ImtiazAtBradley/VIP_Weather/images/unor3.jpg

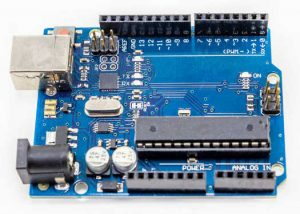
images/unor3.jpg
