ImtiazAtBradley/VIP_Weather/images/antenna-field.gif

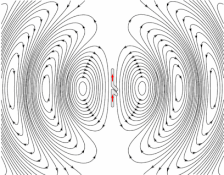
images/antenna-field.gif
