ImtiazAtBradley/VIP_Weather/images/dipole-antenna.gif

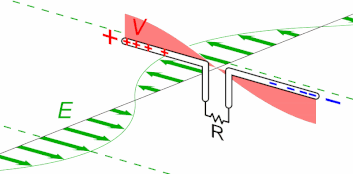
images/dipole-antenna.gif
