ImtiazAtBradley/VIP_Weather/images/esp32block.jpg

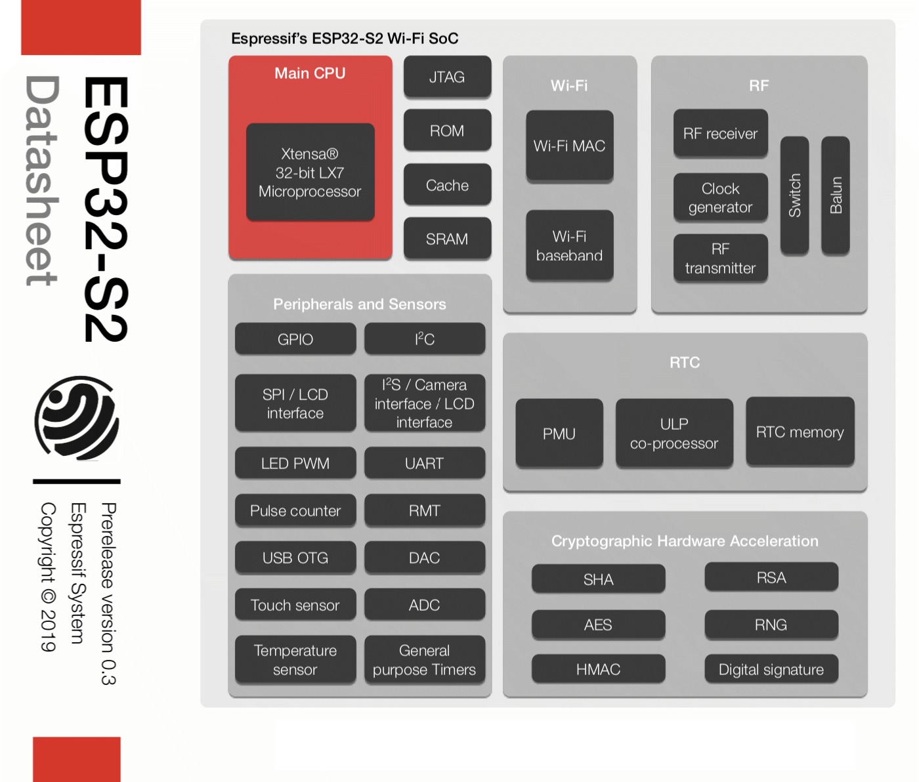
images/esp32block.jpg
