ImtiazAtBradley/VIP_Weather/images/ipv4-address-bytes.png

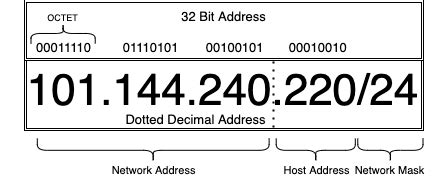
images/ipv4-address-bytes.png
