ImtiazAtBradley/VIP_Weather/images/kicad.png

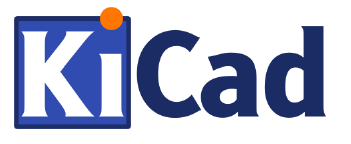
images/kicad.png
