ImtiazAtBradley/VIP_Weather/images/nginx.png

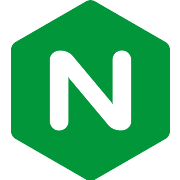
images/nginx.png
