ImtiazAtBradley/VIP_Weather/images/onshape.PNG

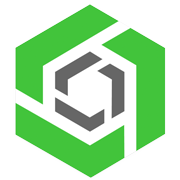
images/onshape.PNG
