ImtiazAtBradley/VIP_Weather/images/redis.png

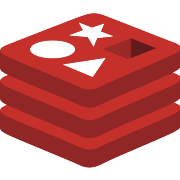
images/redis.png
