ImtiazAtBradley/VIP_Weather/images/ubuntu.png

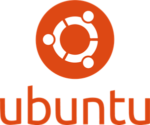
images/ubuntu.png
