ImtiazAtBradley/VIP_Weather/images/weather-station-block.png

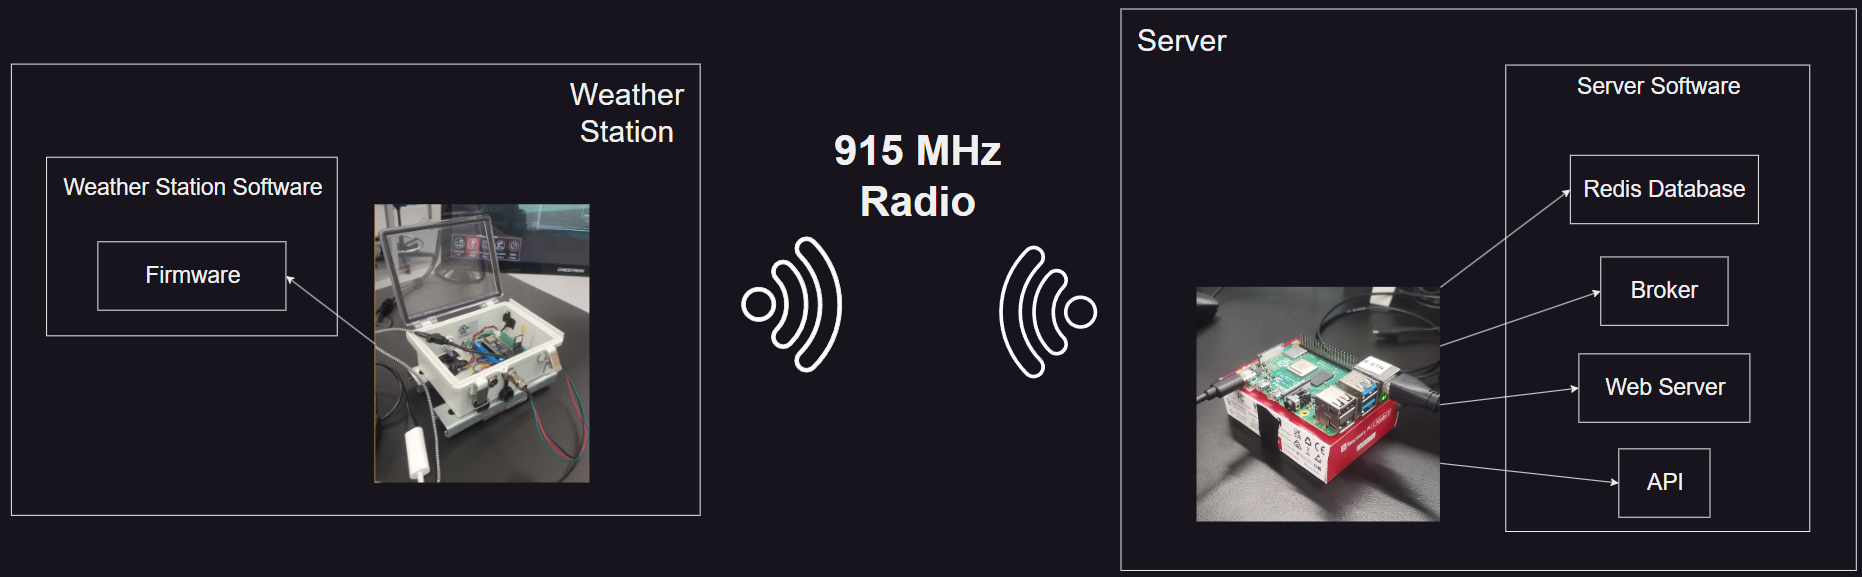
images/weather-station-block.png
