ImtiazAtBradley/VIP_Weather/images/weather-station-website.png

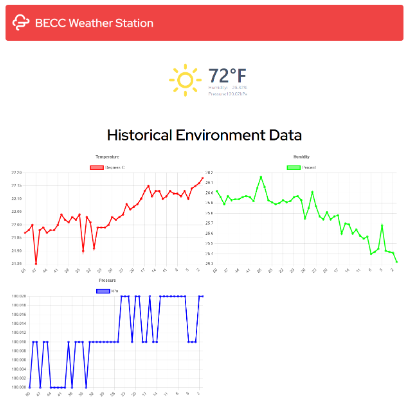
images/weather-station-website.png
