ImtiazAtBradley/VIP_Weather/src/main.cpp

/**
 * @file main.cpp
 * @brief VIP Project weather station source
 * 
 */
#include <Arduino.h>
#include <weather_station.h>

/* ========================================================================== */
/*                        PRIVATE FUNCTION DECLARATIONS                       */
/* ========================================================================== */

/* ========================================================================== */
/*                              STATIC VARIABLES                              */
/* ========================================================================== */

/* ========================================================================== */
/*                                MAIN PROGRAM                                */
/* ========================================================================== */

void setup(){

}

void loop(){

}

/* ========================================================================== */
/*                        PRIVATE FUNCTION DEFINITIONS                        */
/* ========================================================================== */
