ImtiazAtBradley/VIP_Weather/broker/broker/include/constants.h

#pragma once

namespace bc_broker
{
   namespace version
   {
      constexpr static int major = 1;
      constexpr static int minor = 1;
      constexpr static int patch = 0;
   } // namespace version
} // namespace bc_broker
