ImtiazAtBradley/VIP_Weather/broker/broker/include/utils.h

#pragma once

#include <stdint.h>
#include <string>
#include <optional>

int64_t GetUnixTimestamp();
std::string GetIso8601Time();

bool FileExists(const std::string fileName);


std::optional<std::string> GetFileContent(std::string filePath);
